Gyrohammer/commapogo/component_data/usb_connector/GT-USB-7001C/GT-USB-7001C.pdf

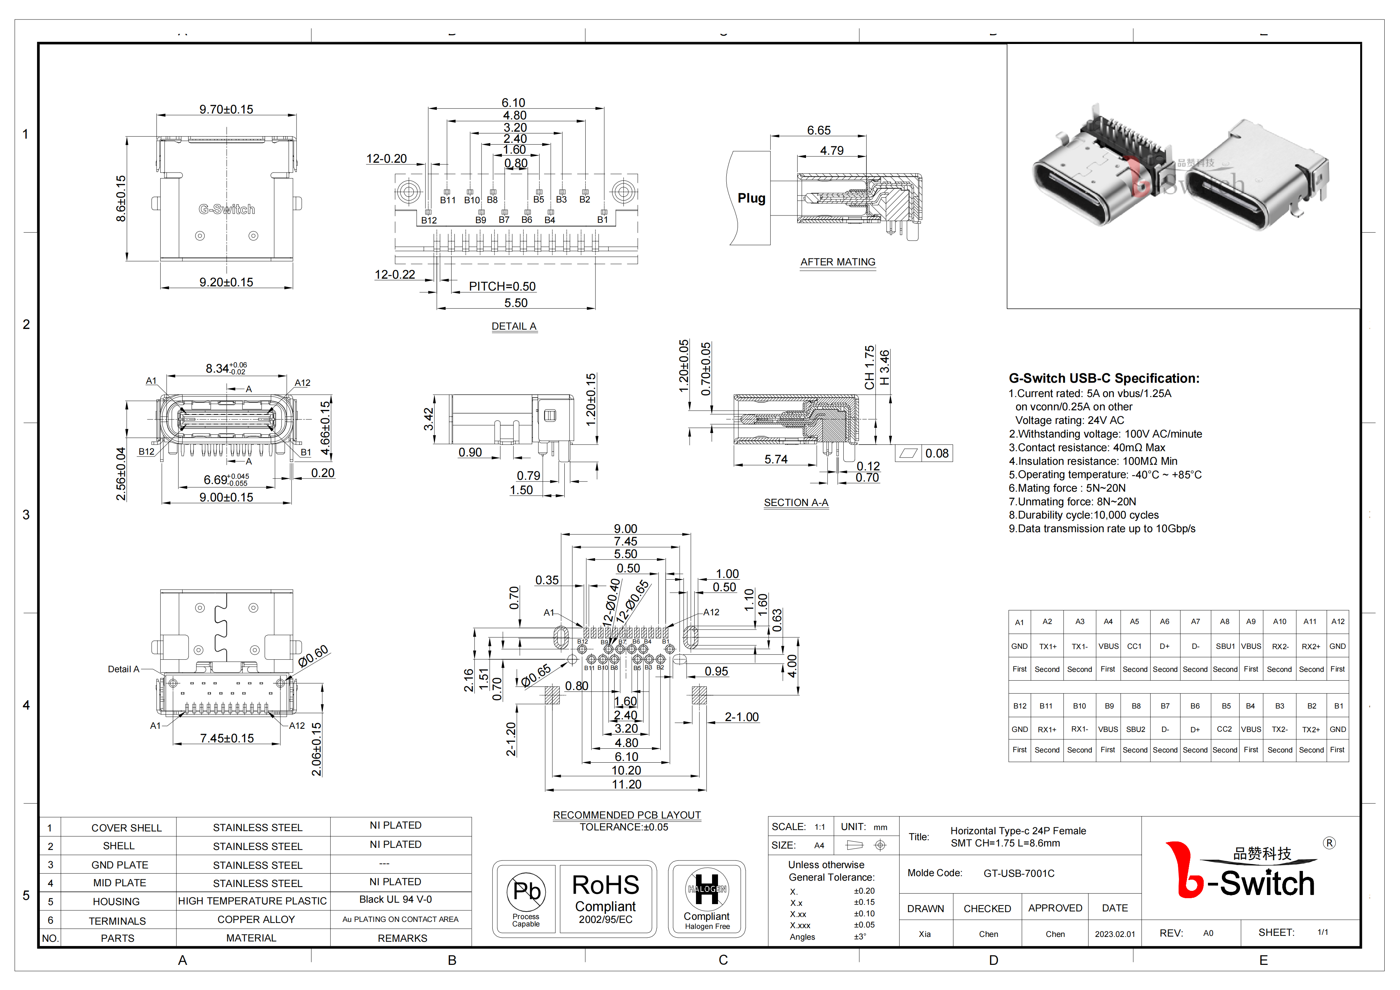
[picture p6: page 1]
