Gyrohammer/commapogo/3d files/pre-fab_parts/2906-4-15-20-75-14-11-0.step

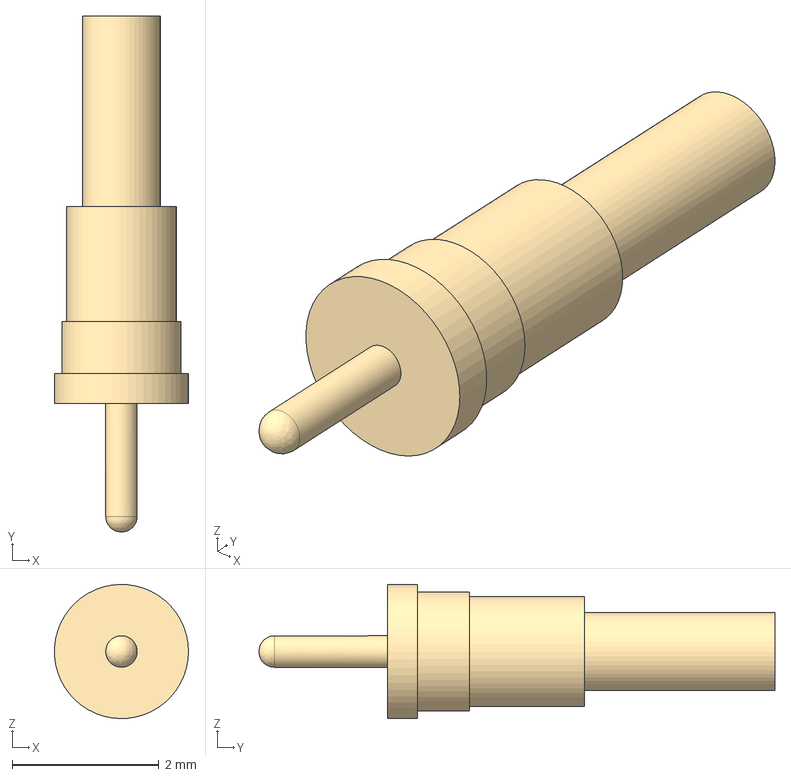
[picture p22: CAD file, 2024-02-16]
3d files/pre-fab_parts/2906-4-15-20-75-14-11-0.step
1.83 x 7.04 x 1.83 mm
