Gyrohammer/commapogo/3d files/prototype_Gravimatrix/gravimatrix_d73/unit_side.stl

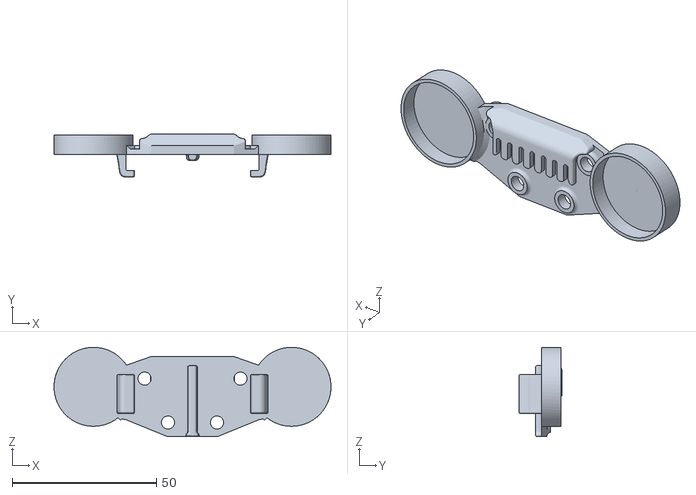
[picture p23: CAD file, 2024-02-16]
3d files/prototype_Gravimatrix/gravimatrix_d73/unit_side.stl
96.1 x 15.0 x 31.0
