Gyrohammer/commapogo/3d files/prototype_Gravimatrix/gravimatrix_d83/unit_side_v2.stl

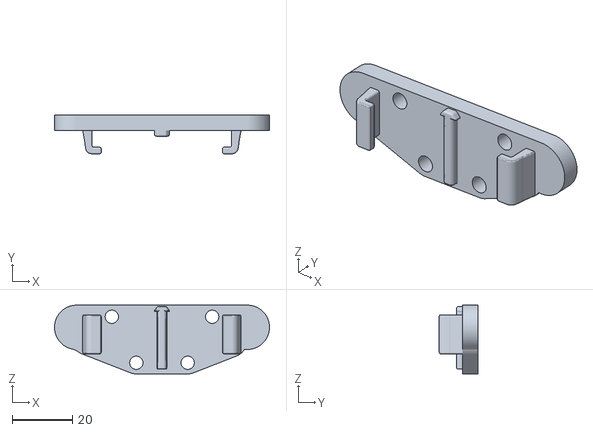
[picture p24: CAD file, 2024-03-12]
3d files/prototype_Gravimatrix/gravimatrix_d83/unit_side_v2.stl
71.3 x 12.8 x 22.8
