Gyrohammer/commapogo/3d files/prototype_Gravimatrix/gravimatrix_dc3/windshield_side.stl

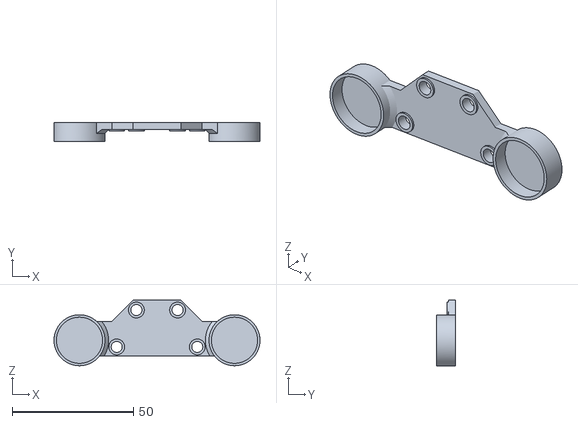
[picture p25: CAD file, 2024-02-19]
3d files/prototype_Gravimatrix/gravimatrix_dc3/windshield_side.stl
85.1 x 7.66 x 27.1
