Gyrohammer/commapogo/3d files/prototype_Gravimatrix/gravimatrix_dx03/unit_side.stl

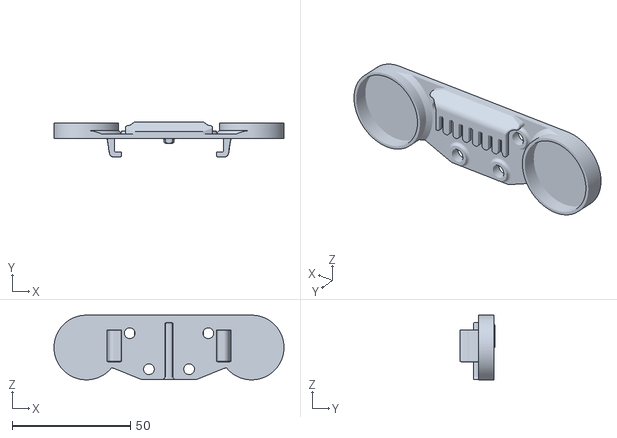
[picture p26: CAD file, 2024-02-19]
3d files/prototype_Gravimatrix/gravimatrix_dx03/unit_side.stl
97.4 x 15.0 x 27.4
