Gyrohammer/commapogo/3d files/prototype_Gravimatrix/unit_side_slotted.stl

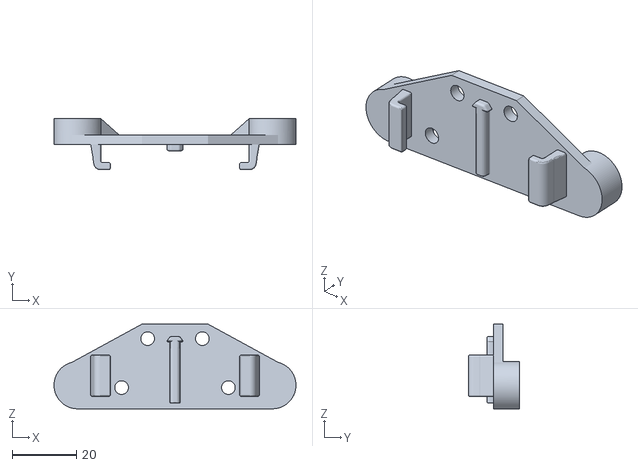
[picture p27: CAD file, 2024-04-05]
3d files/prototype_Gravimatrix/unit_side_slotted.stl
75.4 x 15.9 x 26.4
