Gyrohammer/commapogo/3d files/prototype_polaron/windshield mount .stl

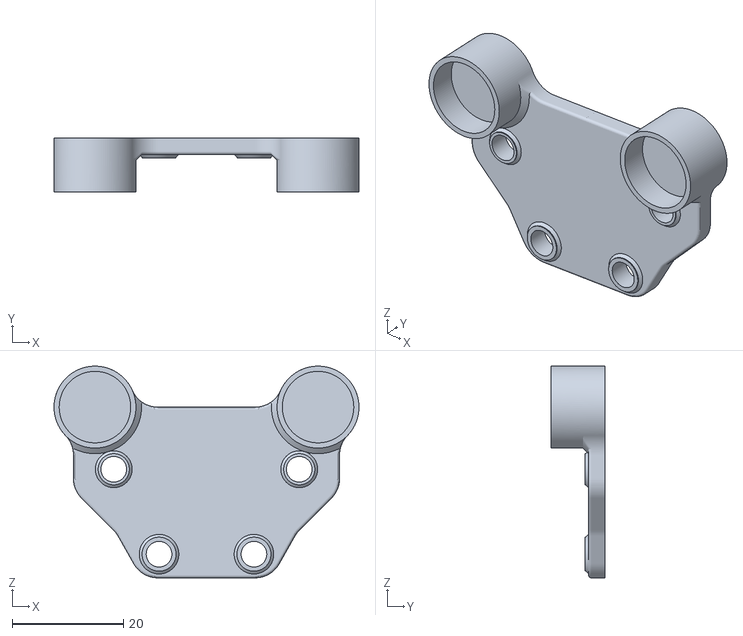
[picture p28: CAD file, 2024-02-22]
3d files/prototype_polaron/windshield mount .stl
54.7 x 9.76 x 38.0
