Gyrohammer/commapogo/testing_equipment/cable_tester/usb3cablecheck.stl

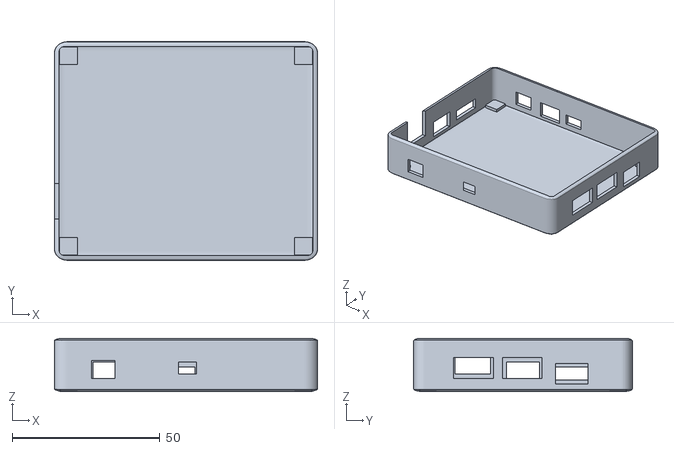
[picture p29: CAD file, 2024-02-21]
testing_equipment/cable_tester/usb3cablecheck.stl
89.0 x 74.0 x 18.0
