Gyrohammer/commapogo/3d files/pre-fab_parts/pcb.stl

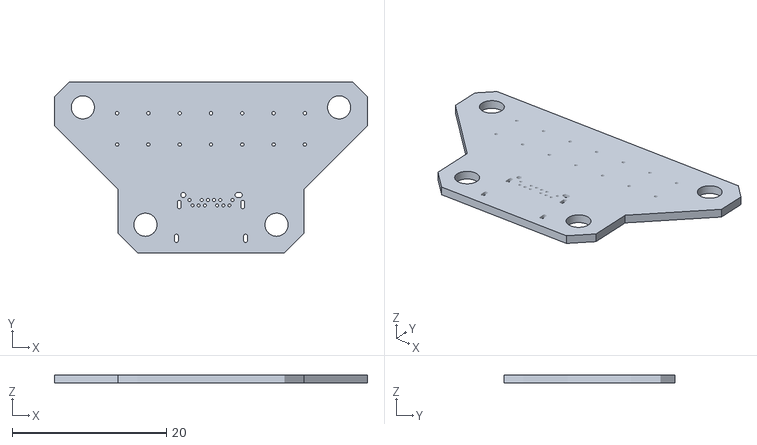
[picture p30: CAD file, 2024-02-14]
3d files/pre-fab_parts/pcb.stl
40.6 x 22.2 x 1.07
