Gyrohammer/commapogo/3d files/prototype_Gravimatrix/unit_side_short_threaded.stl

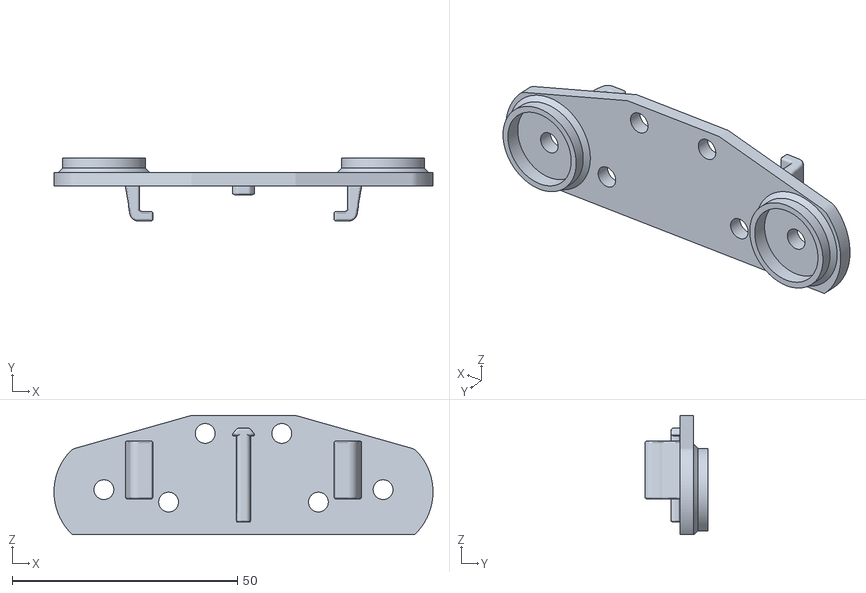
[picture p31: CAD file, 2024-03-20]
3d files/prototype_Gravimatrix/unit_side_short_threaded.stl
84.2 x 14.1 x 26.5
