Gyrohammer/commapogo/3d files/testing_jig/Upper.stl

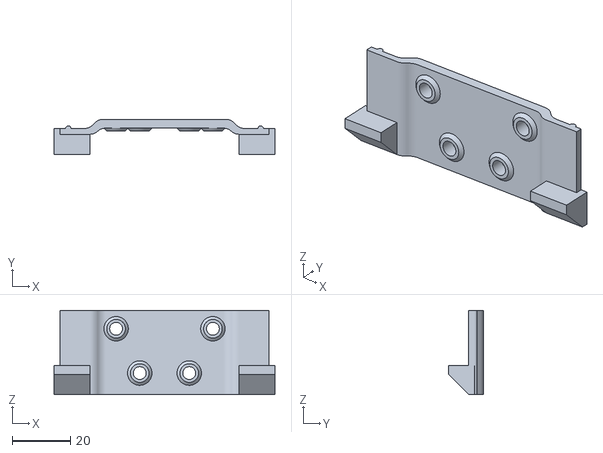
[picture p32: CAD file, 2024-04-05]
3d files/testing_jig/Upper.stl
76.0 x 12.1 x 29.0
