Gyrohammer/commapogo/testing_equipment/cable_tester/usb3cablecheckdeckelsicht.stl

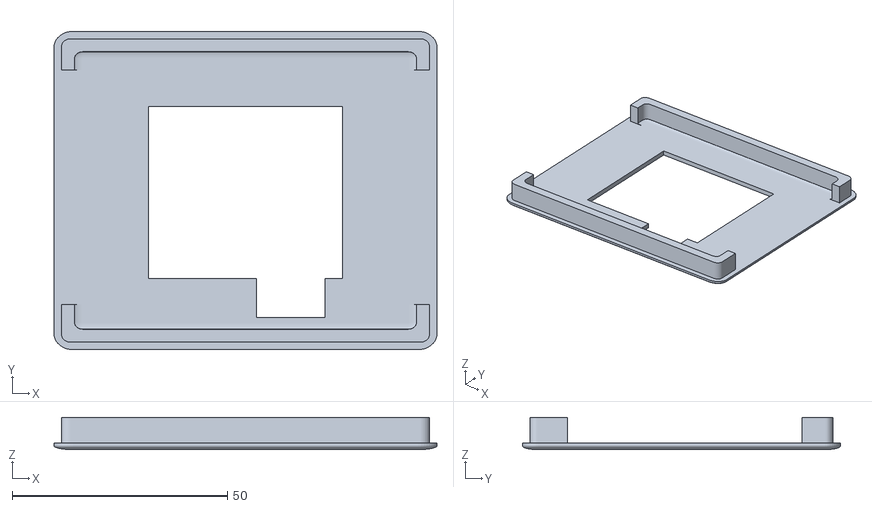
[picture p33: CAD file, 2024-02-21]
testing_equipment/cable_tester/usb3cablecheckdeckelsicht.stl
89.0 x 74.0 x 7.50
