Gyrohammer/commapogo/3d files/pre-fab_parts/3X_mount.stl

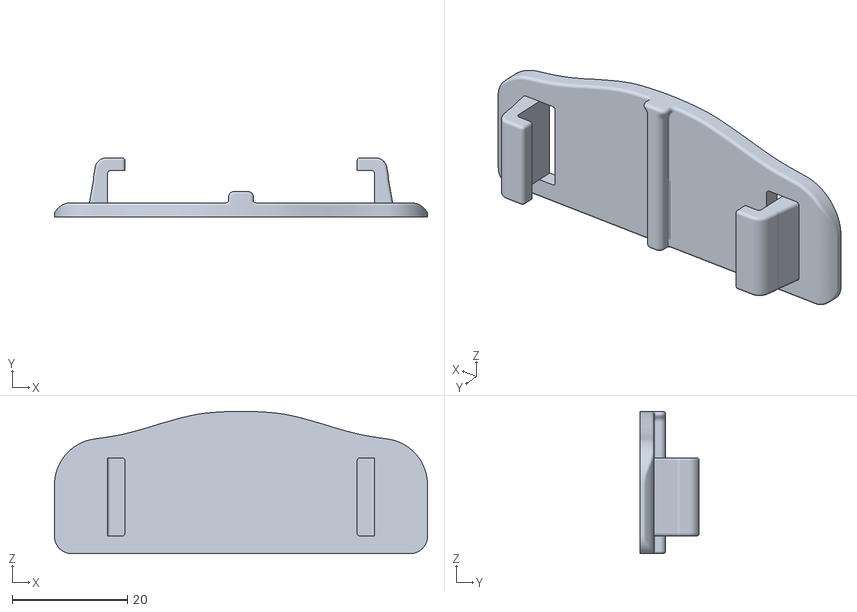
[picture p34: CAD file, 2024-02-13]
3d files/pre-fab_parts/3X_mount.stl
64.6 x 10.3 x 24.7
