Gyrohammer/commapogo/3d files/prototype_Gravimatrix/windshield_side_short_threaded.stl

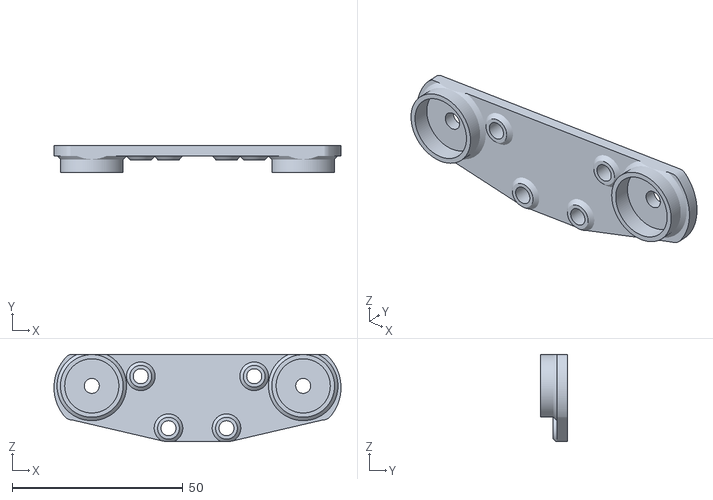
[picture p35: CAD file, 2024-03-20]
3d files/prototype_Gravimatrix/windshield_side_short_threaded.stl
84.2 x 7.77 x 25.5
