Gyrohammer/commapogo/3d files/testing_jig/Lower.stl

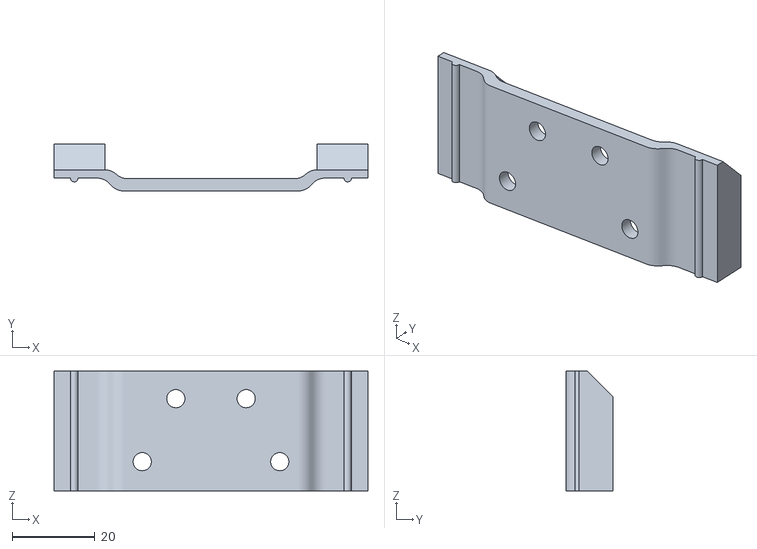
[picture p36: CAD file, 2024-04-05]
3d files/testing_jig/Lower.stl
76.0 x 11.4 x 29.0
