Gyrohammer/commapogo/3d files/pre-fab_parts/USB4056-03-A_REVA2.step

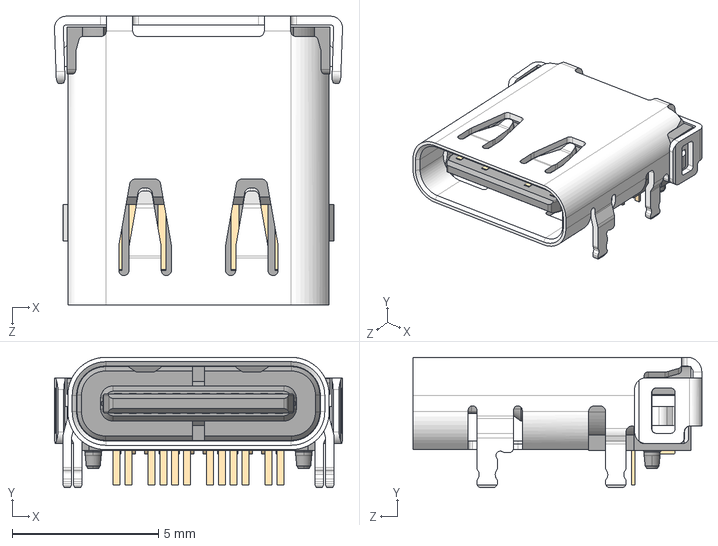
[picture p37: CAD file, 2024-02-07]
3d files/pre-fab_parts/USB4056-03-A_REVA2.step
9.85 x 4.46 x 9.87 mm
