Gyrohammer/commapogo/3d files/prototype_Gravimatrix/windshield_side_short.stl

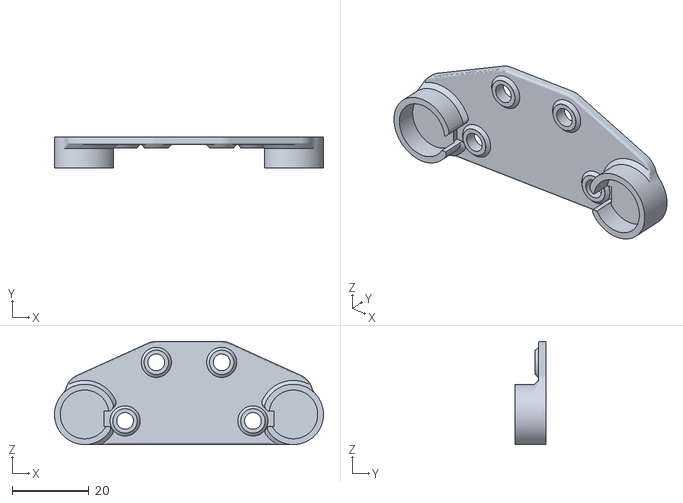
[picture p38: CAD file, 2024-03-18]
3d files/prototype_Gravimatrix/windshield_side_short.stl
70.0 x 7.96 x 26.8
