Gyrohammer/commapogo/3d files/pogo_jigs/pogo_pin_jig_1p50offset_thick.stl

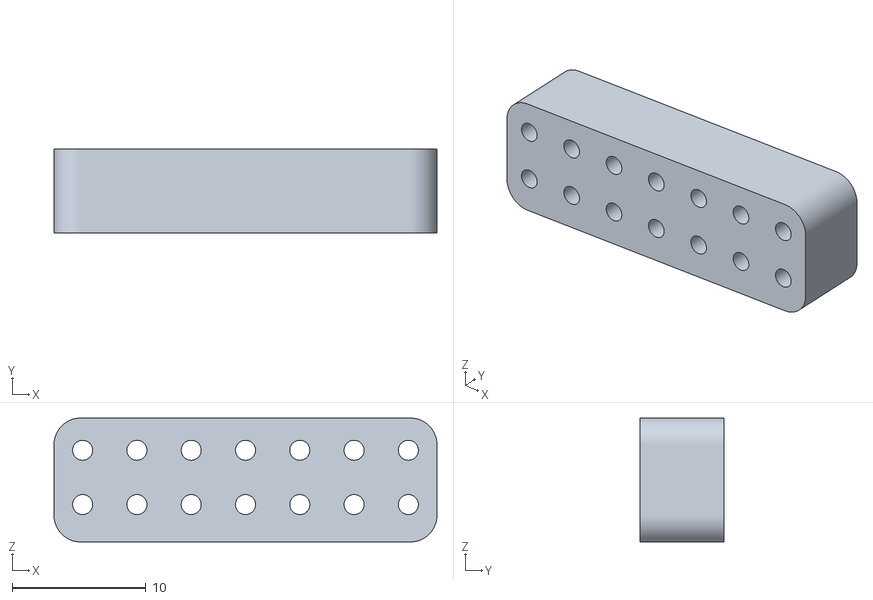
[picture p39: CAD file, 2024-03-15]
3d files/pogo_jigs/pogo_pin_jig_1p50offset_thick.stl
28.7 x 6.30 x 9.28
