Gyrohammer/commapogo/3d files/prototype_Gravimatrix/unit_side_short.stl

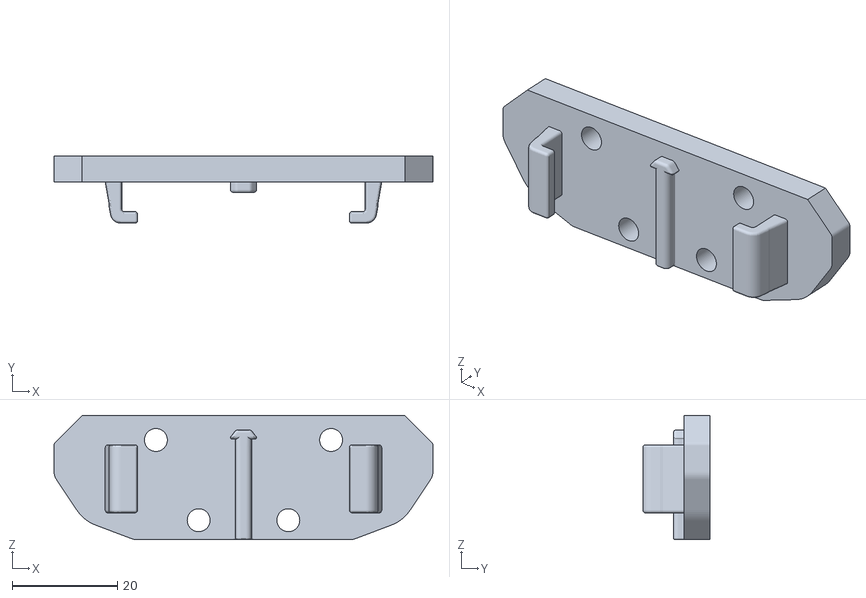
[picture p40: CAD file, 2024-03-18]
3d files/prototype_Gravimatrix/unit_side_short.stl
72.0 x 12.8 x 23.6
