Gyrohammer/commapogo/3d files/pogo_jigs/pogo_pin_jig_1p50offset.stl

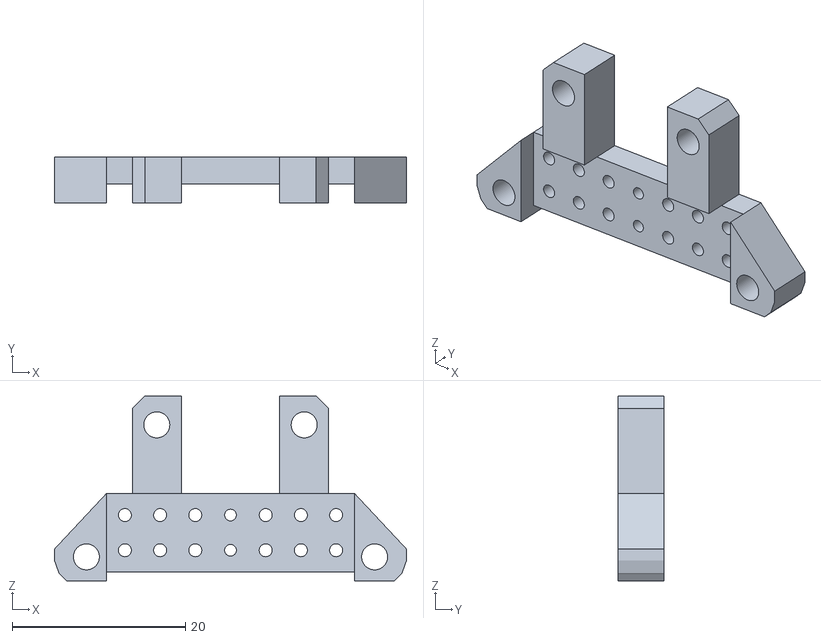
[picture p41: CAD file, 2024-03-15]
3d files/pogo_jigs/pogo_pin_jig_1p50offset.stl
40.6 x 5.30 x 21.4
