Gyrohammer/commapogo/3d files/prototype_Gravimatrix/windshield_side.stl

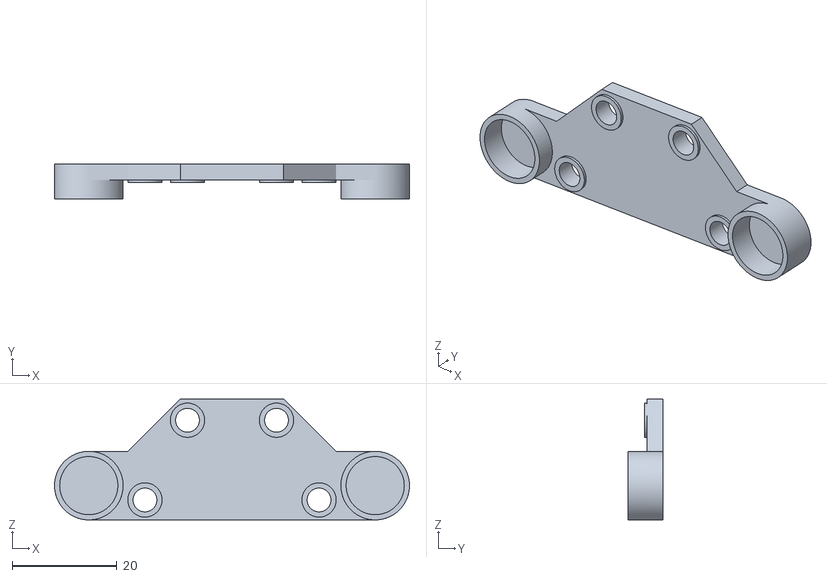
[picture p42: CAD file, 2024-02-14]
3d files/prototype_Gravimatrix/windshield_side.stl
67.8 x 6.66 x 23.1
