Gyrohammer/commapogo/3d files/prototype_Gravimatrix/unit_side.stl

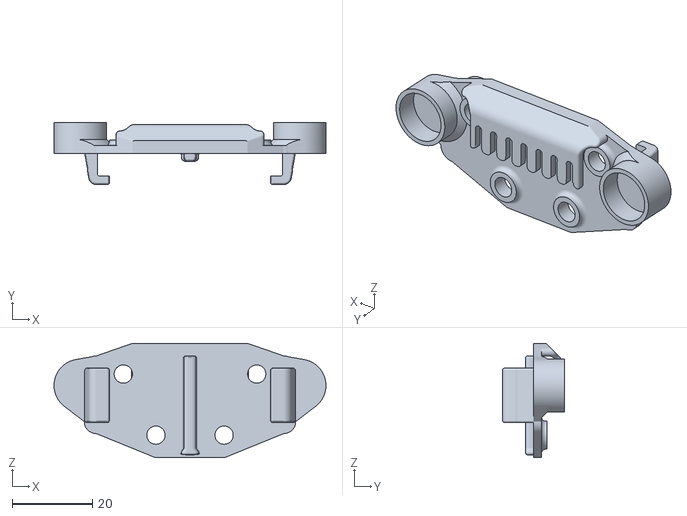
[picture p44: CAD file, 2024-02-14]
3d files/prototype_Gravimatrix/unit_side.stl
67.8 x 15.6 x 28.5
