Gyrohammer/commapogo/3d files/pogo_jigs/pogo_pin_jig_1p600_thick.stl

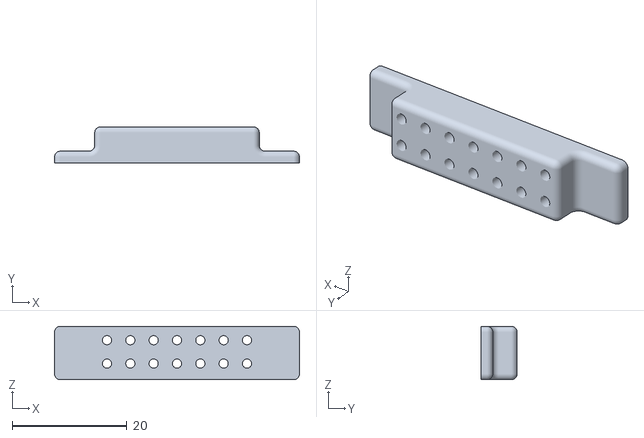
[picture p45: CAD file, 2024-03-13]
3d files/pogo_jigs/pogo_pin_jig_1p600_thick.stl
42.7 x 6.30 x 9.28
