Gyrohammer/commapogo/3d files/pogo_jigs/pogo_pin_jig_1p400_thin.stl

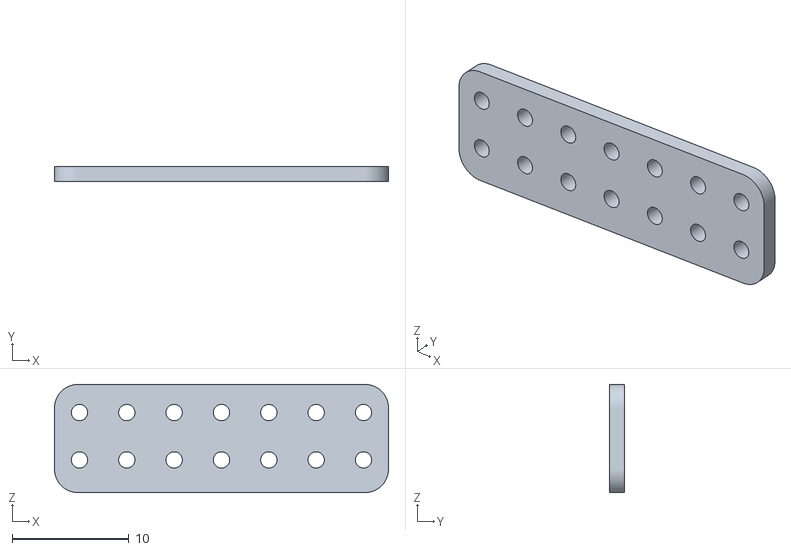
[picture p46: CAD file, 2024-03-12]
3d files/pogo_jigs/pogo_pin_jig_1p400_thin.stl
28.7 x 1.30 x 9.28
