Gyrohammer/commapogo/3d files/pogo_jigs/pogo_pin_jig_1p250.stl

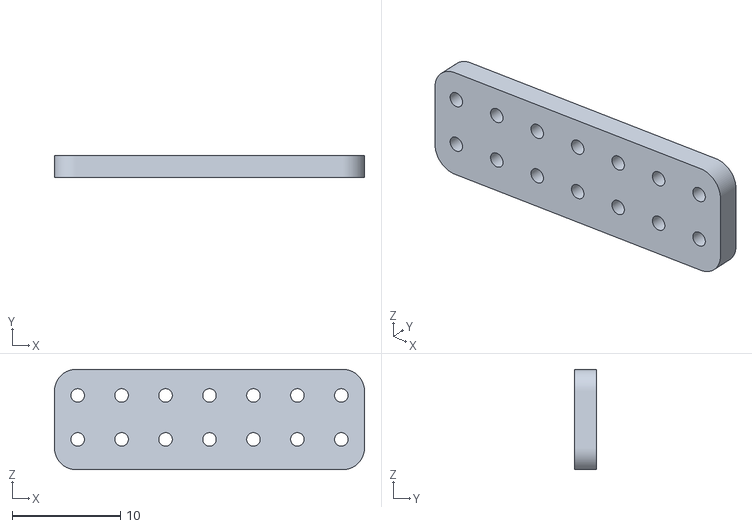
[picture p47: CAD file, 2024-03-11]
3d files/pogo_jigs/pogo_pin_jig_1p250.stl
28.7 x 2.00 x 9.28
