Gyrohammer/commapogo/testing_equipment/cable_tester/NextDocument.jpg

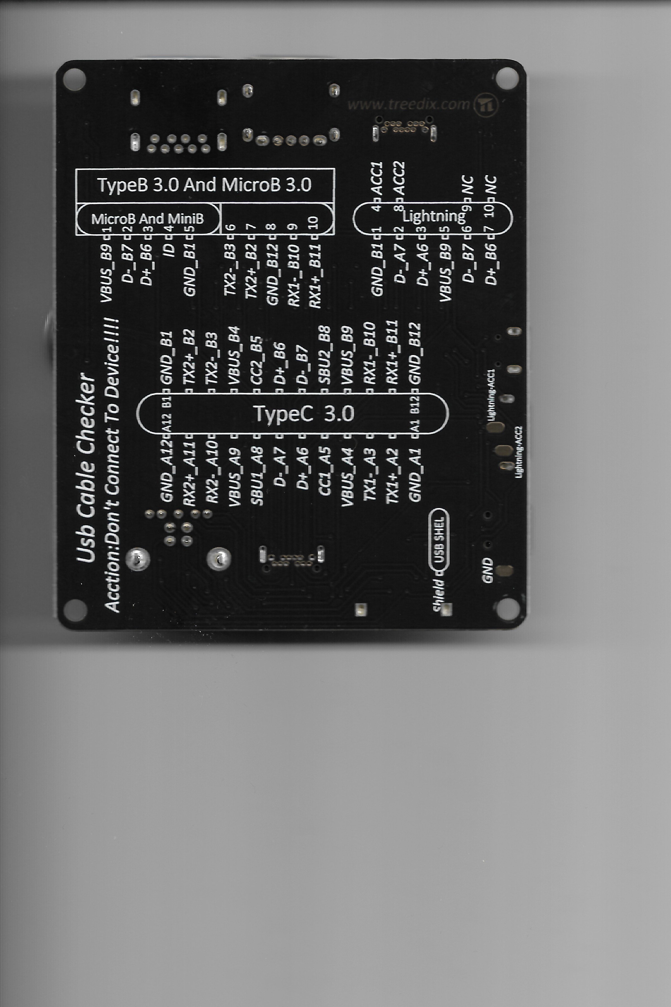
testing_equipment/cable_tester/NextDocument.jpg
