Gyrohammer/commapogo/OBD-C.sch.pdf

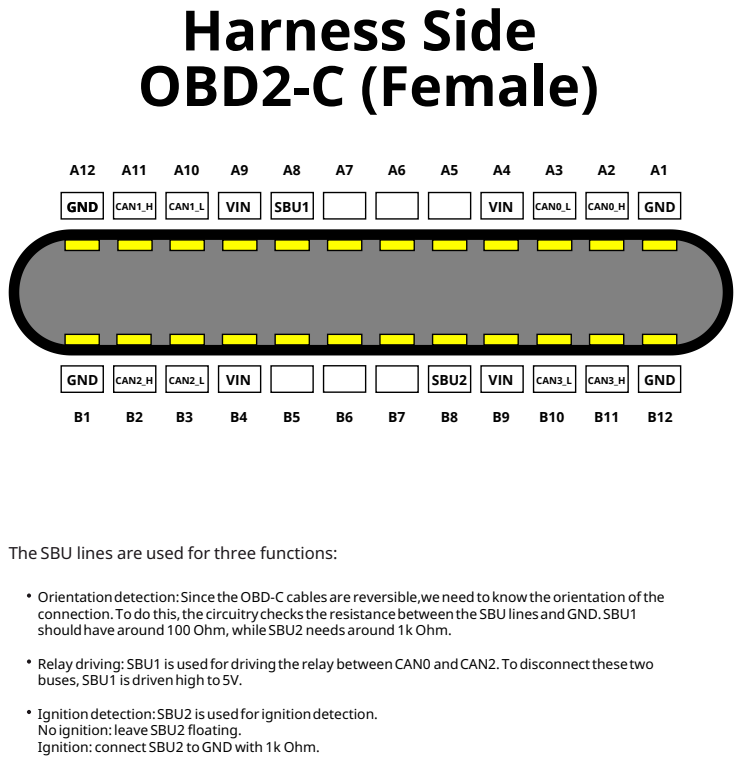
[picture p50: page 1]
GND; VIN; SBU2 VIN; GND CAN1_H CAN1_L; SBU1; VIN CAN0_L; CAN2_H CAN2_L; CAN3_L CAN3_H; CAN0_H; Harness Side OBD2-C (Female)

The SBU lines are used for three functions:

Orientationdetection:Sincethe OBD-C cables are reversible,weneedtoknowthe orientation ofthe
connection.Todo this,the circuitrychecks the resistancebetweenthe SBU linesandGND.SBU1
shouldhave around 100 Ohm, whileSBU2 needs around 1k Ohm.
Relay driving: SBU1 is usedfordrivingthe relay betweenCAN0 andCAN2.Todisconnectthesetwo
buses, SBU1 is drivenhigh to5V.
Ignitiondetection:SBU2 is usedfor ignitiondetection.
Noignition: leave SBU2 floating.
Ignition: connect SBU2 toGND with 1k Ohm.
