Gyrohammer/commapogo/female_top_view.pdf

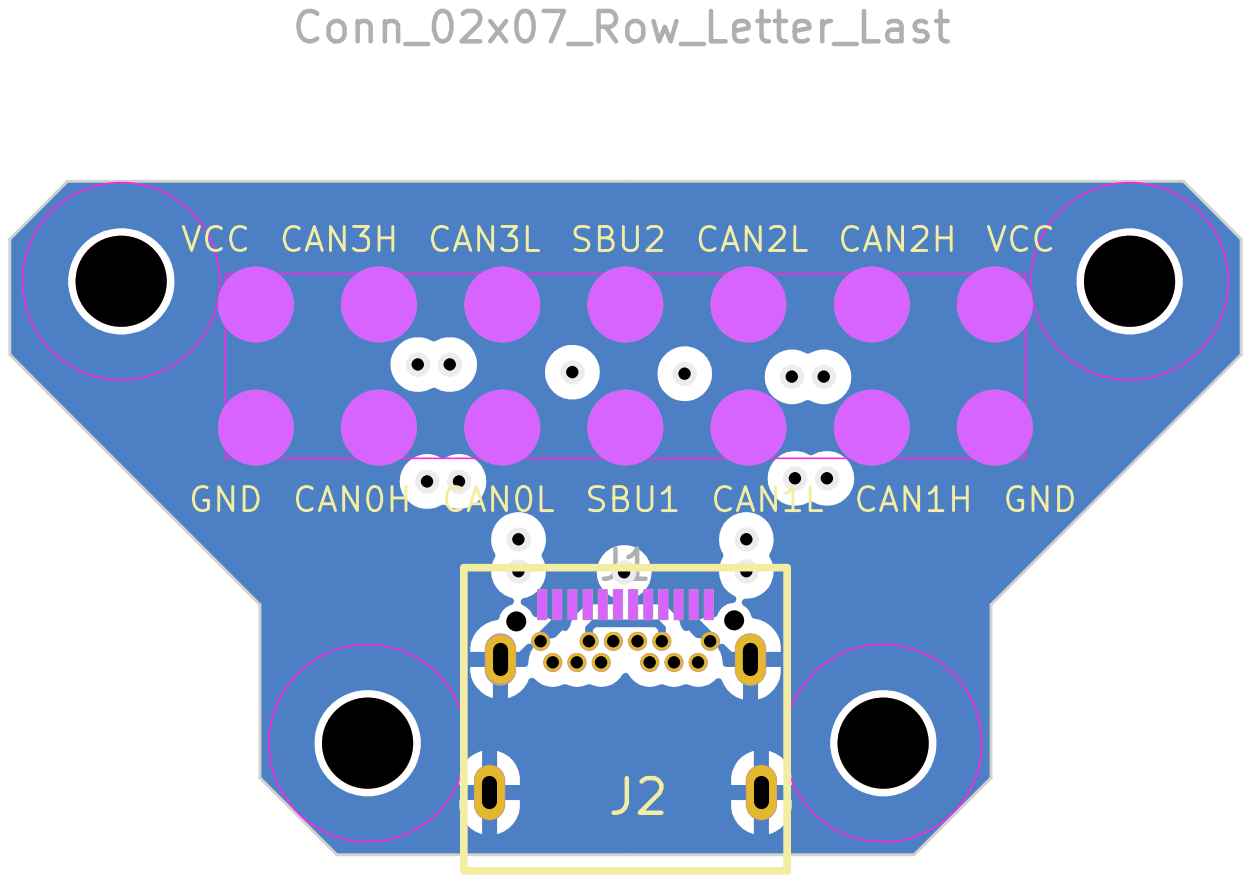
[picture p52: page 1]
