Gyrohammer/commapogo/male_top_view.pdf

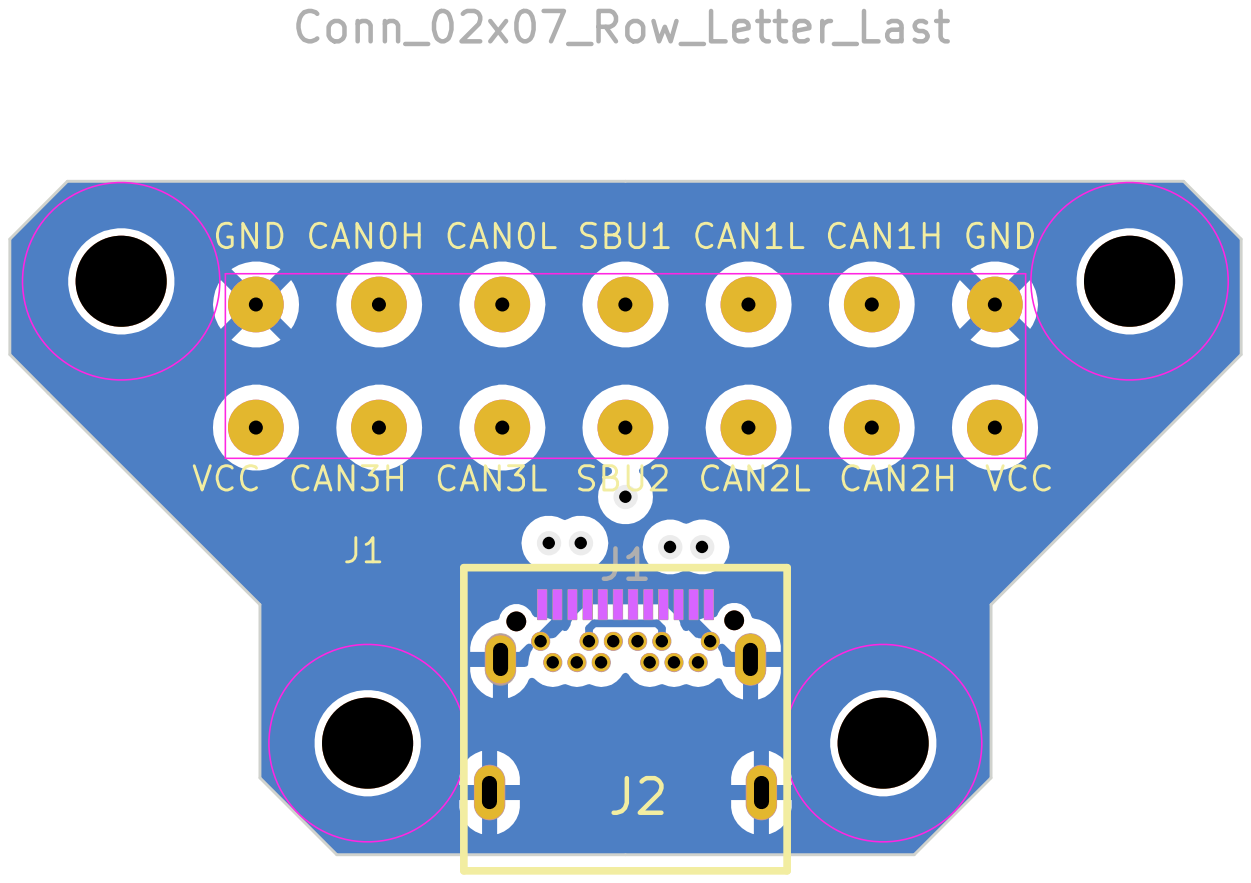
[picture p53: page 1]
